aelevine99/NumitronClock/numitron breakout/render_iso4.png

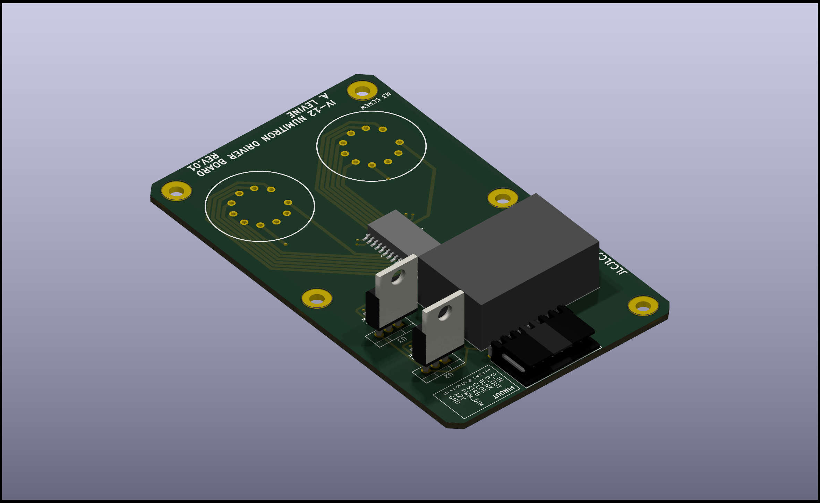
numitron breakout/render_iso4.png
