aelevine99/NumitronClock/numitron breakout/render_iso.png

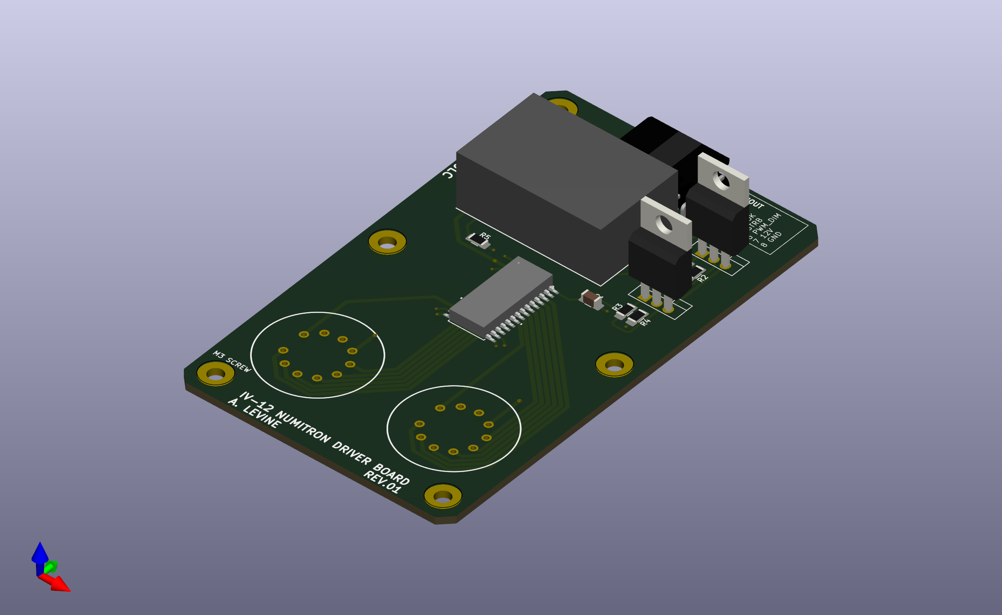
numitron breakout/render_iso.png
